Philip-Kiehnle/PowerSensorEmulator/python/chintPM/chintPM.py

"""The Chint pm  Integration."""
import asyncio
import logging
import threading
from datetime import timedelta
from typing import TypedDict, TypeVar, Optional, Any, Final
from types import MappingProxyType
from collections.abc import (
    # Callable,
    Mapping,
)

# import homeassistant.helpers.config_validation as cv
# import voluptuous as vol
from collections.abc import Awaitable, Callable
# from homeassistant.config_entries import ConfigEntry
# from homeassistant.const import (
#     CONF_HOST,
#     CONF_PORT,
#     Platform,
# )
CONF_HOST: Final = "host"
CONF_PORT: Final = "port"

class ConfigEntry:
    """Hold a configuration entry."""

    entry_id: str
    domain: str
    title: str
    data: MappingProxyType[str, Any]

    def __init__(
        self,
        *,
        data: Mapping[str, Any],
    ) -> None:
        """Initialize a config entry."""
        _setter = object.__setattr__

        # Config data
        _setter(self, "data", MappingProxyType(data))

    def __setattr__(self, key: str, value: Any) -> None:
        """Set an attribute."""
        super().__setattr__(key, value)
        self.clear_cache()


# from homeassistant.core import HomeAssistant, callback
# from homeassistant.helpers.event import async_track_time_interval
# from homeassistant.helpers.debounce import Debouncer
# from homeassistant.helpers.entity import DeviceInfo, Entity
# from homeassistant.helpers.update_coordinator import DataUpdateCoordinator, UpdateFailed

import async_timeout

from pymodbus.exceptions import ConnectionException, ModbusIOException
from pymodbus.client import (
    AsyncModbusSerialClient,
    AsyncModbusTcpClient,
)
from pymodbus.payload import BinaryPayloadDecoder
from pymodbus.constants import Endian

from .const import (
    CONF_SLAVE_IDS,
    CONF_METER_TYPE,
    DOMAIN,
    DATA_UPDATE_COORDINATORS,
    UPDATE_INTERVAL,
    MeterTypes,
)

_LOGGER = logging.getLogger(__name__)

# PLATFORMS: list[Platform] = [
#     Platform.SENSOR,
# ]

T = TypeVar("T")


class ChintDxsuDevice:
    """Chint pm device object"""

    def __init__(self, entry, scan_interval) -> None:
        """Initialize the Modbus hub."""
        self._entry = entry
        self._lock = threading.Lock()
        self._scan_interval = scan_interval
        self._unsub_interval_method = None
        self._sensors = []
        self.data = {}

    async def update(self, client, unit_id):
        """update sensors"""
        print("update sensors")
        match self._entry.data[CONF_METER_TYPE]:
            case MeterTypes.METER_TYPE_CT_3P:
                await self.read_values_type_normal(client, unit_id)
            case _:
                await self.read_values(client, unit_id)

    async def read_values(self, client, unit_id):
        """read modbus value groups"""
        print("read modbus value groups")
        async def read_header(registers):
            decoder = BinaryPayloadDecoder.fromRegisters(
                registers, byteorder=Endian.BIG
            )
            # REV verison
            self.data["rev"] = decoder.decode_16bit_uint()
            # UCode Programming password codE
            self.data["ucode"] = decoder.decode_16bit_uint()
            # ClrE Electric energy zero clearing CLr.E(1:zero clearing)
            self.data["clre"] = decoder.decode_16bit_uint()
            # net Selecting of the connection mode net(0:3P4W,13P3W)
            self.data["net"] = decoder.decode_16bit_uint()
            decoder.skip_bytes(2 * 2)
            # IrAt Current Transformer Ratio
            self.data["irat"] = decoder.decode_16bit_uint()
            # UrAt Potential Transformer Ratio(*)
            self.data["urat"] = decoder.decode_16bit_uint()
            decoder.skip_bytes(3 * 2)
            # Meter type
            self.data["meter_type"] = decoder.decode_16bit_uint()

        async def read_header_proto(registers):
            decoder = BinaryPayloadDecoder.fromRegisters(
                registers, byteorder=Endian.BIG
            )
            # Protocol Protocol changing-over
            self.data["protocol"] = decoder.decode_16bit_uint()
            # Addr Communication address Addr
            self.data["addr"] = decoder.decode_16bit_uint()
            # bAud Communication baud rate bAud
            self.data["baud"] = decoder.decode_16bit_uint()

            # Secound
            self.data["secound"] = decoder.decode_16bit_uint()
            # Minutes
            self.data["minutes"] = decoder.decode_16bit_uint()
            # Hour
            self.data["hour"] = decoder.decode_16bit_uint()
            # Day
            self.data["day"] = decoder.decode_16bit_uint()
            # Month
            self.data["month"] = decoder.decode_16bit_uint()
            # Year
            self.data["year"] = decoder.decode_16bit_uint()

        async def read_elecricity_power(registers):
            decoder = BinaryPayloadDecoder.fromRegisters(
                registers, byteorder=Endian.BIG
            )

            # Uab Line -line voltage, the unit is V
            self.data["uab"] = decoder.decode_32bit_float()
            # Ubc Line -line voltage, the unit is V
            self.data["ubc"] = decoder.decode_32bit_float()
            # Uca Line -line voltage, the unit is V
            self.data["uca"] = decoder.decode_32bit_float()

            # Ua Phase-phase voltage, the unit is V
            self.data["ua"] = decoder.decode_32bit_float()
            # Ub Phase-phase voltaget, he unit is V
            self.data["ub"] = decoder.decode_32bit_float()
            # Uc Phase-phase voltage, the unit is V
            self.data["uc"] = decoder.decode_32bit_float()

            # Ia The data of three phase current,the unit is A
            self.data["ia"] = decoder.decode_32bit_float()
            # Ib The data of three phase current,the unit is A
            self.data["ib"] = decoder.decode_32bit_float()
            # Ic The data of three phase current,the unit is A
            self.data["ic"] = decoder.decode_32bit_float()

            # Pt Conjunction active power，the unit is W
            self.data["pt"] = decoder.decode_32bit_float()
            # Pa A phase active power，the unit is W
            self.data["pa"] = decoder.decode_32bit_float()
            # Pb B phase active power，the unit is W (invalid when three phase three wire)
            self.data["pb"] = decoder.decode_32bit_float()
            # Pc C phase active power，the unit is W
            self.data["pc"] = decoder.decode_32bit_float()

            # Qt Conjunction reactive power，the unit is var
            self.data["qt"] = decoder.decode_32bit_float()
            # Qa A phase reactive power， the unit is var
            self.data["qa"] = decoder.decode_32bit_float()
            # Qb B phase reactive power， the unit is var (invalid when three phase three wire)
            self.data["qb"] = decoder.decode_32bit_float()
            # Qc C phase reactive power， the unit is var
            self.data["qc"] = decoder.decode_32bit_float()

        async def read_elecricity_factor(registers):
            decoder = BinaryPayloadDecoder.fromRegisters(
                registers, byteorder=Endian.BIG
            )
            # PFt Conjunction power factor
            self.data["pft"] = decoder.decode_32bit_float()
            # Pfa A phase power factor (invalid when three phase three wire)
            self.data["pfa"] = decoder.decode_32bit_float()
            # PFb B phase power factor (invalid when three phase three wire)
            self.data["pfb"] = decoder.decode_32bit_float()
            # PFc C phase power factor (invalid when three phase three wire)
            self.data["pfc"] = decoder.decode_32bit_float()

        async def read_elecricity_other(registers):
            decoder = BinaryPayloadDecoder.fromRegisters(
                registers, byteorder=Endian.BIG
            )
            # Freq Frequency
            self.data["freq"] = decoder.decode_32bit_float()
            decoder.skip_bytes(2 * 4)
            # DmPt Total active power demand
            self.data["dmpt"] = decoder.decode_32bit_float()

        async def read_total(registers):
            decoder = BinaryPayloadDecoder.fromRegisters(
                registers, byteorder=Endian.BIG
            )
            # ImpEp (current)positive active total energy
            self.data["impep"] = decoder.decode_32bit_float()
            decoder.skip_bytes(
                2 * 8
            )  # is reading start 0x401e this line is needed, maybe smart meter "-H" version only problem? --> this line is needed! but start address is wrong in documentation
            # ExpEp (current)negative active total energy
            self.data["expep"] = decoder.decode_32bit_float()

        async def read_quadrant_i(registers):
            decoder = BinaryPayloadDecoder.fromRegisters(
                registers, byteorder=Endian.BIG
            )
            # (current) quadrant I reactive total energy
            self.data["q1eq"] = decoder.decode_32bit_float()

        async def read_quadrant_ii(registers):
            decoder = BinaryPayloadDecoder.fromRegisters(
                registers, byteorder=Endian.BIG
            )
            # (current) quadrant II reactive total energy
            self.data["q2eq"] = decoder.decode_32bit_float()

        async def read_quadrant_iii(registers):
            decoder = BinaryPayloadDecoder.fromRegisters(
                registers, byteorder=Endian.BIG
            )
            # (current) quadrant III reactive total energy
            self.data["q3eq"] = decoder.decode_32bit_float()

        async def read_quadrant_iv(registers):
            decoder = BinaryPayloadDecoder.fromRegisters(
                registers, byteorder=Endian.BIG
            )
            # (current) quadrant IV reactive total energy
            self.data["q4eq"] = decoder.decode_32bit_float()

        if client.connected:
            header = await client.read_holding_registers(
                address=0x0, count=12, slave=unit_id
            )
            header_proto = await client.read_holding_registers(
                address=0x2C, count=9, slave=unit_id
            )
            elecricity_power = await client.read_holding_registers(
                address=0x2000, count=0x22, slave=unit_id
            )
            elecricity_factor = await client.read_holding_registers(
                address=0x202A, count=8, slave=unit_id
            )
            elecricity_other = await client.read_holding_registers(
                address=0x2044, count=8, slave=unit_id
            )
            # documentation say address is 0x401e but this register contain invalid data, maybe only -H version?
            total = await client.read_holding_registers(
                address=0x4026, count=12, slave=unit_id
            )
            # (current) quadrant I reactive total energy
            quadrant_i = await client.read_holding_registers(
                address=0x4032, count=2, slave=unit_id
            )
            # (current) quadrant II reactive total energy
            quadrant_ii = await client.read_holding_registers(
                address=0x403C, count=2, slave=unit_id
            )
            # (current) quadrant III reactive total energy
            quadrant_iii = await client.read_holding_registers(
                address=0x4046, count=2, slave=unit_id
            )
            # (current) quadrant IV reactive total energy
            quadrant_iv = await client.read_holding_registers(
                address=0x4050, count=2, slave=unit_id
            )

            out = await asyncio.gather(
                read_header(header.registers),
                read_header_proto(header_proto.registers),
                read_elecricity_power(elecricity_power.registers),
                read_elecricity_factor(elecricity_factor.registers),
                read_elecricity_other(elecricity_other.registers),
                read_total(total.registers),
                read_quadrant_i(quadrant_i.registers),
                read_quadrant_ii(quadrant_ii.registers),
                read_quadrant_iii(quadrant_iii.registers),
                read_quadrant_iv(quadrant_iv.registers),
                return_exceptions=True,
            )
            # print(out)

    async def read_values_type_normal(self, client, unit_id):
        """read modbus value groups"""

        async def read_header(registers):
            decoder = BinaryPayloadDecoder.fromRegisters(
                registers, byteorder=Endian.BIG
            )
            # REV verison
            self.data["rev"] = decoder.decode_16bit_uint()
            # UCode Programming password codE
            self.data["ucode"] = decoder.decode_16bit_uint()
            # ClrE Electric energy zero clearing CLr.E(1:zero clearing)
            self.data["clre"] = decoder.decode_16bit_uint()
            # net Selecting of the connection mode net(0:3P4W,13P3W)
            self.data["net"] = decoder.decode_16bit_uint()
            decoder.skip_bytes(2 * 2)
            # IrAt Current Transformer Ratio
            self.data["irat"] = decoder.decode_16bit_uint()
            # UrAt Potential Transformer Ratio(*)
            self.data["urat"] = decoder.decode_16bit_uint()

        async def read_header_proto(registers):
            decoder = BinaryPayloadDecoder.fromRegisters(
                registers, byteorder=Endian.BIG
            )
            # Protocol Protocol changing-over
            self.data["protocol"] = decoder.decode_16bit_uint()
            # Addr Communication address Addr
            self.data["baud"] = decoder.decode_16bit_uint()
            # bAud Communication baud rate bAud
            self.data["addr"] = decoder.decode_16bit_uint()

        async def read_elecricity_power(registers):
            decoder = BinaryPayloadDecoder.fromRegisters(
                registers, byteorder=Endian.BIG
            )

            # Uab Line -line voltage, the unit is V
            self.data["uab"] = decoder.decode_32bit_float()
            # Ubc Line -line voltage, the unit is V
            self.data["ubc"] = decoder.decode_32bit_float()
            # Uca Line -line voltage, the unit is V
            self.data["uca"] = decoder.decode_32bit_float()

            # Ua Phase-phase voltage, the unit is V
            self.data["ua"] = decoder.decode_32bit_float()
            # Ub Phase-phase voltaget, he unit is V
            self.data["ub"] = decoder.decode_32bit_float()
            # Uc Phase-phase voltage, the unit is V
            self.data["uc"] = decoder.decode_32bit_float()

            # Ia The data of three phase current,the unit is A
            self.data["ia"] = decoder.decode_32bit_float()
            # Ib The data of three phase current,the unit is A
            self.data["ib"] = decoder.decode_32bit_float()
            # Ic The data of three phase current,the unit is A
            self.data["ic"] = decoder.decode_32bit_float()

            # Pt Conjunction active power，the unit is W
            self.data["pt"] = decoder.decode_32bit_float()
            # Pa A phase active power，the unit is W
            self.data["pa"] = decoder.decode_32bit_float()
            # Pb B phase active power，the unit is W (invalid when three phase three wire)
            self.data["pb"] = decoder.decode_32bit_float()
            # Pc C phase active power，the unit is W
            self.data["pc"] = decoder.decode_32bit_float()

            # Qt Conjunction reactive power，the unit is var
            self.data["qt"] = decoder.decode_32bit_float()
            # Qa A phase reactive power， the unit is var
            self.data["qa"] = decoder.decode_32bit_float()
            # Qb B phase reactive power， the unit is var (invalid when three phase three wire)
            self.data["qb"] = decoder.decode_32bit_float()
            # Qc C phase reactive power， the unit is var
            self.data["qc"] = decoder.decode_32bit_float()

        async def read_elecricity_factor(registers):
            decoder = BinaryPayloadDecoder.fromRegisters(
                registers, byteorder=Endian.BIG
            )
            # PFt Conjunction power factor
            self.data["pft"] = decoder.decode_32bit_float()
            # Pfa A phase power factor (invalid when three phase three wire)
            self.data["pfa"] = decoder.decode_32bit_float()
            # PFb B phase power factor (invalid when three phase three wire)
            self.data["pfb"] = decoder.decode_32bit_float()
            # PFc C phase power factor (invalid when three phase three wire)
            self.data["pfc"] = decoder.decode_32bit_float()

        async def read_elecricity_other(registers):
            decoder = BinaryPayloadDecoder.fromRegisters(
                registers, byteorder=Endian.BIG
            )
            # Freq Frequency
            self.data["freq"] = decoder.decode_32bit_float()

        async def read_total(registers):
            decoder = BinaryPayloadDecoder.fromRegisters(
                registers, byteorder=Endian.BIG
            )
            # ImpEp (current)positive active total energy
            self.data["impep"] = decoder.decode_32bit_float()
            decoder.skip_bytes(2 * 8)
            # ExpEp (current)negative active total energy
            self.data["expep"] = decoder.decode_32bit_float()

        async def read_quadrant_i(registers):
            decoder = BinaryPayloadDecoder.fromRegisters(
                registers, byteorder=Endian.BIG
            )
            # (current) quadrant I reactive total energy
            self.data["q1eq"] = decoder.decode_32bit_float()

        async def read_quadrant_ii(registers):
            decoder = BinaryPayloadDecoder.fromRegisters(
                registers, byteorder=Endian.BIG
            )
            # (current) quadrant II reactive total energy
            self.data["q2eq"] = decoder.decode_32bit_float()

        async def read_quadrant_iii(registers):
            decoder = BinaryPayloadDecoder.fromRegisters(
                registers, byteorder=Endian.BIG
            )
            # (current) quadrant III reactive total energy
            self.data["q3eq"] = decoder.decode_32bit_float()

        async def read_quadrant_iv(registers):
            decoder = BinaryPayloadDecoder.fromRegisters(
                registers, byteorder=Endian.BIG
            )
            # (current) quadrant IV reactive total energy
            self.data["q4eq"] = decoder.decode_32bit_float()

        if client.connected:
            header = await client.read_holding_registers(
                address=0x0, count=12, slave=unit_id
            )
            header_proto = await client.read_holding_registers(
                address=0x2C, count=9, slave=unit_id
            )
            elecricity_power = await client.read_holding_registers(
                address=0x2000, count=0x22, slave=unit_id
            )
            elecricity_factor = await client.read_holding_registers(
                address=0x202A, count=8, slave=unit_id
            )
            elecricity_other = await client.read_holding_registers(
                address=0x2044, count=8, slave=unit_id
            )
            # documentation say address is 0x401e but this register contain invalid data, maybe only -H version?
            total = await client.read_holding_registers(
                address=0x1026, count=12, slave=unit_id
            )
            # (current) quadrant I reactive total energy
            quadrant_i = await client.read_holding_registers(
                address=0x1032, count=2, slave=unit_id
            )
            # (current) quadrant II reactive total energy
            quadrant_ii = await client.read_holding_registers(
                address=0x103C, count=2, slave=unit_id
            )
            # (current) quadrant III reactive total energy
            quadrant_iii = await client.read_holding_registers(
                address=0x1046, count=2, slave=unit_id
            )
            # (current) quadrant IV reactive total energy
            quadrant_iv = await client.read_holding_registers(
                address=0x1050, count=2, slave=unit_id
            )

            await asyncio.gather(
                *[
                    read_header(header.registers),
                    read_header_proto(header_proto.registers),
                    read_elecricity_power(elecricity_power.registers),
                    read_elecricity_factor(elecricity_factor.registers),
                    read_elecricity_other(elecricity_other.registers),
                    read_total(total.registers),
                    read_quadrant_i(quadrant_i.registers),
                    read_quadrant_ii(quadrant_ii.registers),
                    read_quadrant_iii(quadrant_iii.registers),
                    read_quadrant_iv(quadrant_iv.registers),
                ],
                return_exceptions=True,
            )


class ChintUpdateCoordinator():
    """A specialised DataUpdateCoordinator for chint smart meter."""

    def __init__(
        self,
        device: ChintDxsuDevice,
        entry: ConfigEntry,
        update_interval: timedelta | None = None,
        update_method: Callable[[], Awaitable[T]] | None = None,
        # request_refresh_debouncer: Debouncer | None = None,
    ) -> None:
        """Create a ChintUpdateCoordinator."""
        if entry.data[CONF_HOST] is None:
            port_host = ""
            port_name = str(entry.data[CONF_PORT])
        else:
            port_host = "".join(filter(str.isalnum, entry.data[CONF_HOST]))
            port_name = "".join(filter(str.isalnum, str(entry.data[CONF_PORT])))

        # super().__init__(
        #     name=f"{port_host}_{port_name}_{entry.data[CONF_SLAVE_IDS][0]}_data_update_coordinator",
        #     update_interval=update_interval,
        #     update_method=update_method,
        #     # request_refresh_debouncer=request_refresh_debouncer,
        # )
        self.device = device
        self._client: AsyncModbusSerialClient | AsyncModbusTcpClient
        self._unit_id = entry.data[CONF_SLAVE_IDS][0]
        self._entry = entry

    async def push_sensor_read(self, address, count, data_type):
        # TODO: push device addresses to read
        await self._client.read_holding_registers(
            address=address, count=count, slave=self._unit_id
        )
        self.device._sensors.append(1)

    async def create_client(self, port, host):
        """create one clinet object whole update cordinator"""
        try:
            if host is None:
                self._client = AsyncModbusSerialClient(
                    port=port,
                    baudrate=9600,
                    bytesize=8,
                    stopbits=1,
                    parity="N",
                )
            else:
                self._client = AsyncModbusTcpClient(host=host, port=port, timeout=5)

            # self._client.connect()
        except Exception as err:
            # always try to stop the bridge, as it will keep retrying
            # in the background otherwise!
            if self._client is not None:
                self._client.close()

            raise err

    async def async_update_data(self):
    # async def _async_update_data(self):
        try:
            if not self._client.connected:
                await self._client.connect()
            else:
                # check alive
                try:
                    await self._client.read_holding_registers(
                        address=0x0, count=1, slave=self._unit_id
                    )
                except ModbusIOException as merr:
                    # merr.isError()
                    await self._client.connect()

            async with async_timeout.timeout(30):
                return await self.device.update(self._client, self._unit_id)
        except Exception as err:
            print("Could not update values {err}")
            #raise UpdateFailed(f"Could not update values: {err}") from err

    # @property
    # def device_info(self) -> DeviceInfo:
    #     """Return device information about this pm device."""
    #     # _LOGGER.debug(self.coordinator.config_entry.data)
    #     match self._entry.data[CONF_METER_TYPE]:
    #         case MeterTypes.METER_TYPE_CT_3P:
    #             meter_type_name = "DTSU-666"
    #         case _:
    #             meter_type_name = "DTSU-666-H"
    #     return DeviceInfo(
    #         identifiers={(DOMAIN, self._entry.entry_id)},
    #         name=self._entry.title,
    #         manufacturer="Chint",
    #         model=meter_type_name,
    #     )

    async def stop(self):
        """Close the modbus connection"""
        await self._client.close()


async def async_setup_entry(entry: ConfigEntry):
    """Set up a chint mobus."""
    device = ChintDxsuDevice(
        entry,
        UPDATE_INTERVAL,
    )

    update_coordinators = []

    update_coordinators.append(
        await _create_update_coordinator(device, entry, UPDATE_INTERVAL)
    )

    #await hass.config_entries.async_forward_entry_setups(entry, PLATFORMS)
    # await async_setup_services(hass, entry, device)
    #return True
    return update_coordinators[0]


async def _create_update_coordinator(
    device: ChintDxsuDevice,
    entry: ConfigEntry,
    update_interval,
):
    coordinator = ChintUpdateCoordinator(
        device=device,
        entry=entry,
        update_interval=update_interval,
    )

    await coordinator.create_client(entry.data[CONF_PORT], entry.data[CONF_HOST])

    #await coordinator.async_config_entry_first_refresh()

    return device, coordinator
