Philip-Kiehnle/PowerSensorEmulator/STM32_Code/STM32_PowerSensorEmulator/Core/Src/modbus.c

/**
 * stModbus Libary: A tiny Modbus implementation for Modbus ASCII/RTU
 * Copyright (c) 2017+ [Iurii Bell] ds@inbox.ru (http://www.bel-tech.ru/)
 * All rights reserved.
 *
 * [MIT License](http://www.opensource.org/licenses/mit-license.php)
 *
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
 * @copyright   Copyright (C) 2017+
 * @author      Iurii Bell (ds@inbox.ru)
 * @license     MIT
 * @package     stModbus
 */

#ifdef __cplusplus
extern "C" {
#endif

#include "modbus.h"

#include <stdio.h>
#include <string.h>

// Global variable for modbus context
_stmodbus_context_t g_mbusContext[STMODBUS_COUNT_CONTEXT];
Modbus_ResponseType    g_userError = MBUS_RESPONSE_OK;

void lock() {}

void unlock() {}

/*
 * function mbus_open()
 * open new modbus context for new port
 * return: MODBUS_ERROR - if can't open context
 */
mbus_t mbus_open(Modbus_Conf_t *pconf) {
  mbus_t context;
  for (context = 0; context < STMODBUS_COUNT_CONTEXT; context++) {
    if (g_mbusContext[context].open == 0) {
      break;
    }
  }
  if (context == STMODBUS_COUNT_CONTEXT)
    return (mbus_t)MBUS_ERROR;
  // Clear context
  memset(&g_mbusContext[context], 0, sizeof(_stmodbus_context_t));
  // Copy config to context
  memcpy((void *)&g_mbusContext[context].conf, (void *)pconf,
         sizeof(Modbus_Conf_t));

  g_mbusContext[context].open = 1;
  return context;
}

mbus_status_t mbus_flush(const mbus_t context) {
  g_mbusContext[context].crc16 = 0xFFFF;
  g_mbusContext[context].state = MBUS_STATE_IDLE;
  return MBUS_OK;
}

mbus_status_t mbus_response(mbus_t mb_context, Modbus_ResponseType response) {

  if (response != MBUS_RESPONSE_OK) {
    return mbus_send_error(mb_context, response);
  } else {
  }
  return MBUS_ERROR;
}

uint16_t mbus_error(Modbus_ResponseType error) {
    g_userError = error;
    return 0;
}

inline mbus_status_t mbus_poll_response(mbus_t mb_context) {
  stmbCallBackFunc func = 0;
  _stmodbus_context_t *ctx = &g_mbusContext[mb_context];
  int read = 1, la;
  uint16_t d;

  if (ctx->header.func == 0x04) {
    la = 10;
  }

#if STMODBUS_COUNT_FUNC > 0
  for (int i = 0; i < STMODBUS_COUNT_FUNC; i++) {
    if ((ctx->func[i].code == ctx->response.func)) {
      func = ctx->func[i].func;
      break;
    }
  }
#endif
  switch (ctx->header.func) {
  case MBUS_FUNC_WRITE_COILS:
  case MBUS_FUNC_READ_COILS:
    if ((ctx->header.num == 0) || (ctx->header.num > 0x07D0)) {
      return mbus_response(mb_context, MBUS_RESPONSE_ILLEGAL_DATA_VALUE);
    }
    if ((ctx->header.addr + ctx->header.num) >= ctx->conf.coils) {
      return mbus_response(mb_context, MBUS_RESPONSE_ILLEGAL_DATA_ADDRESS);
    }
    break;
  case MBUS_FUNC_READ_DISCRETE:
    if ((ctx->header.num == 0) || (ctx->header.num > 0x07D0)) {
      return mbus_response(mb_context, MBUS_RESPONSE_ILLEGAL_DATA_VALUE);
    }
    if ((ctx->header.addr + ctx->header.num) > ctx->conf.discrete) {
      return mbus_response(mb_context, MBUS_RESPONSE_ILLEGAL_DATA_ADDRESS);
    }
    break;
  default:
    break;
  }

  if (func != 0) {
    return func(mb_context);
  }

  la = mbus_proto_address((Modbus_ConnectFuncType)ctx->header.func, (int*)&read);
  if (la > 0) {
    la += ctx->header.addr;
  }
  if (la < 60001) {  // power sensor has high address
  //if (la < 50001) {
    ctx->conf.sendbuf[0] = ctx->header.devaddr;
    ctx->conf.sendbuf[1] = ctx->header.func;
    ctx->conf.sendbuf[2] = ctx->header.num * 2;
    if (read && ctx->conf.read) {
      g_userError = MBUS_RESPONSE_OK;
      for (int i = 0; i < ctx->header.num; i++) {
        
        d = ctx->conf.read(la + i);
        ctx->conf.sendbuf[3 + (i << 1)] = d >> 8;
        ctx->conf.sendbuf[3 + (i << 1) + 1] = d & 0xFF;
      }
      if (g_userError == MBUS_RESPONSE_OK) {
          return mbus_send_data(mb_context, 3 + ctx->conf.sendbuf[2]);
      }else {
          return mbus_response(mb_context, g_userError);
      }
    } else if (ctx->conf.write) {
      uint16_t *value;
      ctx->conf.sendbuf[2] = 0;
      switch (ctx->header.func) {
      case MBUS_FUNC_WRITE_REG:
      case MBUS_FUNC_WRITE_COIL:
        // in both these cases, we should return the same packet that we
        // received. in both cases, the packes have 6 bytes of data + 2 CRC
        // bytes = 8 bytes
        value = (uint16_t *)ctx->conf.recvbuf;
        ctx->conf.write(la, *value);
        ctx->conf.sendbuf[2] = ctx->header.addr >> 8;
        ctx->conf.sendbuf[3] = ctx->header.addr & 0xFF;
        ctx->conf.sendbuf[4] = ctx->conf.recvbuf[1];
        ctx->conf.sendbuf[5] = ctx->conf.recvbuf[0];
        return mbus_send_data(mb_context, 6);

      case MBUS_FUNC_WRITE_REGS:
        value = (uint16_t *)ctx->conf.recvbuf;
        for (int i = 0; i < ctx->header.num; i++) {
          ctx->conf.write(la + i, *value++);
        }
        ctx->conf.sendbuf[2] = ctx->header.addr >> 8;
        ctx->conf.sendbuf[3] = ctx->header.addr & 0xFF;
        ctx->conf.sendbuf[4] = ctx->header.num >> 8;
        ctx->conf.sendbuf[5] = ctx->header.num & 0xFF;
        return mbus_send_data(mb_context, 6);
      } // end of switch
    }
  }
  return mbus_response(mb_context, MBUS_RESPONSE_ILLEGAL_FUNCTION);
}

//#include <windows.h>
/*
 * function mbus_close()
 * close modbus context
 * return: none
 */
mbus_status_t mbus_poll(mbus_t mb_context, uint8_t byte) {
  // State machine
  _stmodbus_context_t *ctx = &g_mbusContext[mb_context];

  if (mbus_tickcount() - ctx->timer > 2) {  // reset after 2ms
  //if (mbus_tickcount() - ctx->timer > 50) {  // reset after 50ms
    mbus_flush(mb_context);
  }
  ctx->timer = mbus_tickcount();

  switch (ctx->state) {
  case MBUS_STATE_IDLE:
    mbus_flush(mb_context);
    ctx->state = MBUS_STATE_FUNCTION;
    ctx->header.devaddr = byte;
    break;
  case MBUS_STATE_FUNCTION:
    ctx->header.func = byte;
    switch (byte) {
    case MBUS_FUNC_WRITE_REG:
      ctx->header.rnum = 1;
      ctx->header.num = 1;
      ctx->state = MBUS_STATE_REGADDR_HI;
      break;
    case MBUS_FUNC_WRITE_REGS:
    case MBUS_FUNC_WRITE_COILS:
      ctx->header.rnum = 1;
      ctx->header.num = 0;
      ctx->state = MBUS_STATE_REGADDR_HI;
      break;
    case MBUS_FUNC_READ_INPUT_REGS:
    case MBUS_FUNC_READ_COILS:
    case MBUS_FUNC_READ_REGS:
      ctx->state = MBUS_STATE_REGADDR_HI;
      ctx->header.rnum = 0;
      ctx->header.num = 0;
      break;
    case MBUS_FUNC_WRITE_COIL:
      ctx->header.rnum = 1;
      ctx->header.num = 1;
      ctx->state = MBUS_STATE_REGADDR_HI;
      break;
    default:
      // ctx->state = MBUS_STATE_IDLE;
      mbus_flush(mb_context);
      break;
    }
    break;
  case MBUS_STATE_REGADDR_HI:
    ctx->state = MBUS_STATE_REGADDR_LO;
    ctx->header.addr = byte << 8;
    break;
  case MBUS_STATE_REGADDR_LO:
    ctx->header.addr |= byte;
    if (ctx->header.num == 1 && ctx->header.rnum == 1) {
      ctx->state = MBUS_STATE_DATA_HI;
    } else {
      ctx->state = MBUS_STATE_REGNUM_HI;
    }
    break;
  case MBUS_STATE_DATA_HI:
    ctx->state = MBUS_STATE_DATA_LO;
    ctx->conf.recvbuf[2 * (ctx->header.num - ctx->header.rnum) + 1] = byte;
    break;
  case MBUS_STATE_DATA_LO:
    ctx->conf.recvbuf[2 * (ctx->header.num - ctx->header.rnum)] = byte;
    ctx->header.rnum--;
    if (ctx->header.rnum == 0) {
      ctx->state = MBUS_STATE_CRC_LO;
    } else {
      ctx->state = MBUS_STATE_DATA_HI;
    }
    break;
  case MBUS_STATE_DATA_SIZE:
    ctx->state = MBUS_STATE_DATA;
    ctx->header.size = byte;
    ctx->header.rsize = byte;
    break;
  case MBUS_STATE_DATA:
    ctx->conf.recvbuf[ctx->header.size - ctx->header.rsize] = byte;
    ctx->header.rsize--;
    if (ctx->header.rsize == 0) {
      ctx->state = MBUS_STATE_CRC_LO;
    }
    break;
  case MBUS_STATE_REGNUM_HI:
    ctx->state = MBUS_STATE_REGNUM_LO;
    ctx->header.num = byte << 8;
    break;
  case MBUS_STATE_REGNUM_LO:
    ctx->state = MBUS_STATE_CRC_LO;
    ctx->header.num |= byte;
    if (ctx->header.rnum == 0) {
      ctx->state = MBUS_STATE_CRC_LO;
    } else {
      ctx->header.rnum = ctx->header.num;
      ctx->state = MBUS_STATE_DATA_HI;
      if (ctx->header.func == MBUS_FUNC_WRITE_REGS) {
        ctx->state = MBUS_STATE_DATA_SIZE;
      }
    }

    break;
  case MBUS_STATE_CRC_LO:
    ctx->state = MBUS_STATE_CRC_HI;
    break;
  case MBUS_STATE_CRC_HI:
    ctx->state = MBUS_STATE_FINISH;
    break;
  // We can't processing any more before callback not returned
  case MBUS_STATE_RESPONSE:
    return MBUS_ERROR;
  default:
    mbus_flush(mb_context);
    break;
  }

  ctx->crc16 = mbus_crc16(ctx->crc16, byte);

  if (ctx->state == MBUS_STATE_FINISH) {
    // CRC error
    if (ctx->crc16 != 0) {
      mbus_flush(mb_context);
      return MBUS_ERROR;
    }

    // TODO: Add broadcast messages
    if (ctx->header.devaddr == ctx->conf.devaddr) {
      ctx->state = MBUS_STATE_RESPONSE;
      if (mbus_poll_response(mb_context) == MBUS_OK) {
        mbus_flush(mb_context);
        return MBUS_OK;
      }
      mbus_flush(mb_context);
      return MBUS_ERROR;
    }
    mbus_flush(mb_context);
  }
  return MBUS_OK;
}

mbus_context_t mbus_device(mbus_t mb_context) {
  return (mbus_context_t)&g_mbusContext[mb_context];
}

mbus_context_t mbus_context(mbus_t mb_context) {
  if (g_mbusContext[mb_context].open)
    return (mbus_context_t)&g_mbusContext[mb_context];
  return 0;
}

mbus_status_t mbus_send_error(mbus_t mb_context, Modbus_ResponseType response) {
  uint16_t *pbuf = (uint16_t *)(g_mbusContext[mb_context].conf.sendbuf + 2);
  *pbuf = 0x8300 | (uint8_t)response;
  return mbus_send_data(mb_context, 4);
}

mbus_status_t mbus_send_data(mbus_t mb_context, uint16_t size) {
  // if size > ( conf.send_sz-2) error
  uint16_t crc32 = 0xFFFF;
  const _stmodbus_context_t *ctx = &g_mbusContext[mb_context];
  uint8_t *pbuf = ctx->conf.sendbuf;
  if (ctx->conf.send == 0 || pbuf == 0 || ctx->conf.sendbuf_sz < (size + 2))
    return MBUS_ERROR;
  for (int i = 0; i < size; i++) {
    crc32 = mbus_crc16(crc32, pbuf[i]);
  }
  pbuf[size++] = crc32 & 0xFF;
  pbuf[size++] = (crc32 >> 8);

  if (ctx->conf.send(mb_context, pbuf, size) != size)
    return MBUS_ERROR;
  return MBUS_OK;
}

mbus_status_t mbus_connect(const mbus_t mb_context, stmbCallBackFunc func,
                           Modbus_ConnectFuncType type) {
#if STMODBUS_COUNT_FUNC > 0
  _stmodbus_context_t *ctx = &g_mbusContext[mb_context];
  for (int i = 0; i < STMODBUS_COUNT_FUNC; i++) {
    if ((ctx->func[i].code == 0)) {
      ctx->func[i].func = func;
      ctx->func[i].code = (uint8_t)type;
      return MBUS_OK;
    }
  }
#endif
  return MBUS_ERROR;
}

int mbus_proto_address( Modbus_ConnectFuncType func, int *r) {
  int adr = 0;
  *r = 1;
  switch (func) {
  case MBUS_FUNC_WRITE_REG:
  case MBUS_FUNC_WRITE_REGS:
  case MBUS_FUNC_READ_WRITE_MASK_REGS:
  case MBUS_FUNC_READ_WRITE_REGS:
    *r = 0;
  case MBUS_FUNC_READ_REGS:
    adr = 40001;
    break;
  case MBUS_FUNC_READ_INPUT_REGS:
    adr = 30001;
    break;
  case MBUS_FUNC_READ_DISCRETE:
    adr = 10001;
    break;
  case MBUS_FUNC_WRITE_COILS:
  case MBUS_FUNC_WRITE_COIL:
    *r = 0;
  case MBUS_FUNC_READ_COILS:
    adr = 0001;
    break;
  default:
    break;
  }
  return adr;
}

#ifdef __cplusplus
}
#endif
